floris-dh/ParticleDetector/Data/Am241_Data/fit_plot_0000.png

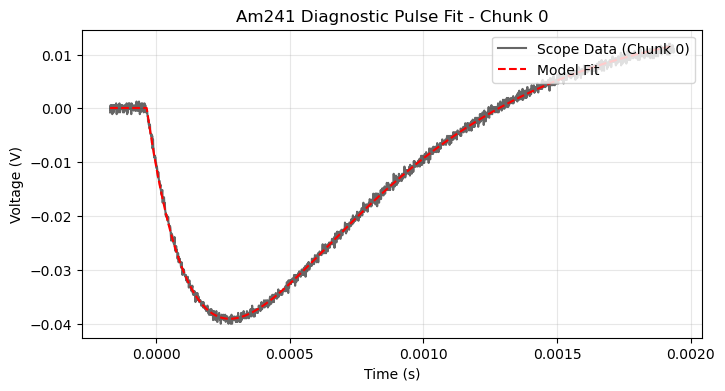
Data/Am241_Data/fit_plot_0000.png
