floris-dh/ParticleDetector/Data/Am241_Data/fit_plot_0002.png

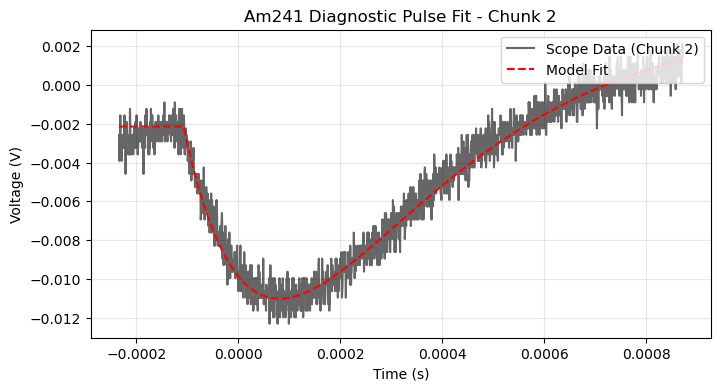
Data/Am241_Data/fit_plot_0002.png
