floris-dh/ParticleDetector/Data/Pu239_Data/fit_plot_0000.png

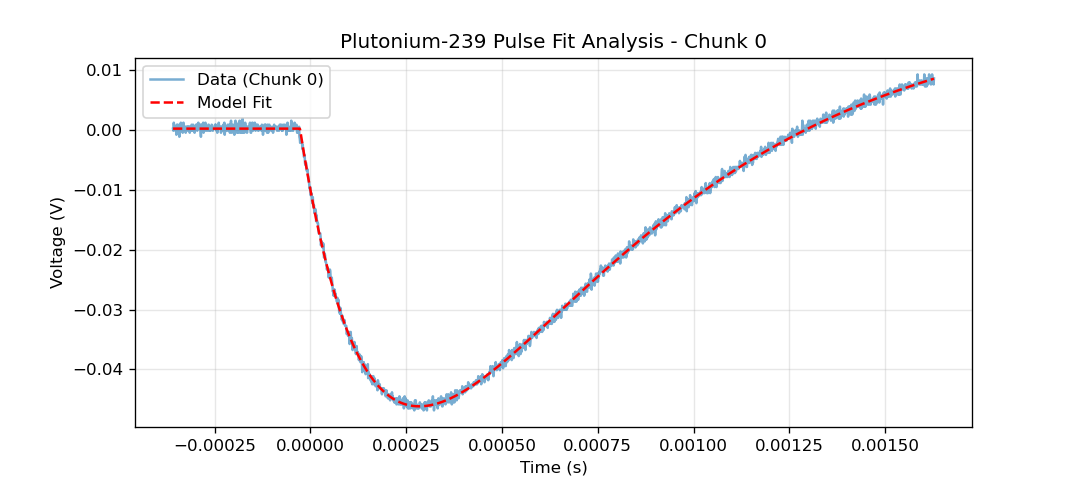
Data/Pu239_Data/fit_plot_0000.png
