floris-dh/ParticleDetector/Data/Ra226_Data/fit_plot_0000.png

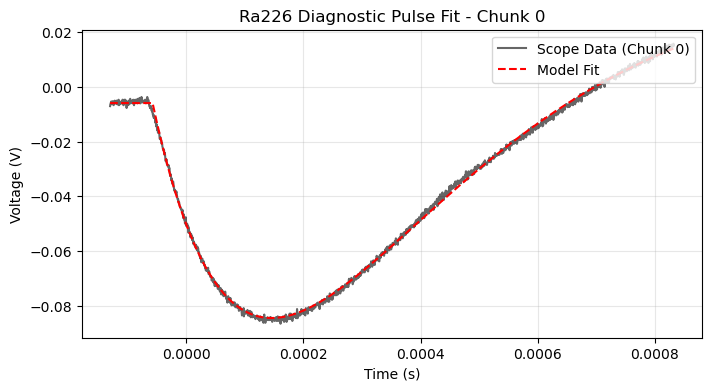
Data/Ra226_Data/fit_plot_0000.png
