floris-dh/ParticleDetector/Data/Ra226_Data/informative_pulses.png

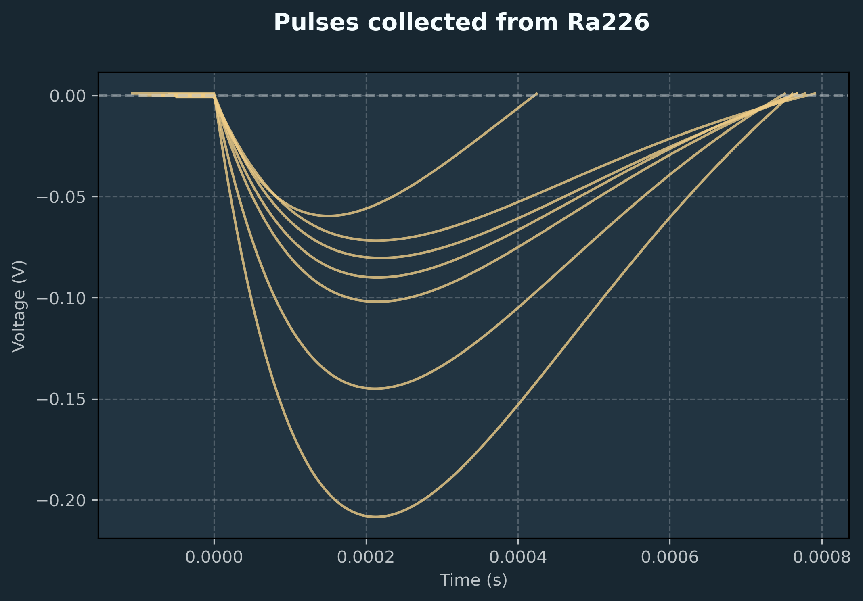
Data/Ra226_Data/informative_pulses.png
